Rotnam/PiTrac/docs/assets/images/camera/image3.jpg

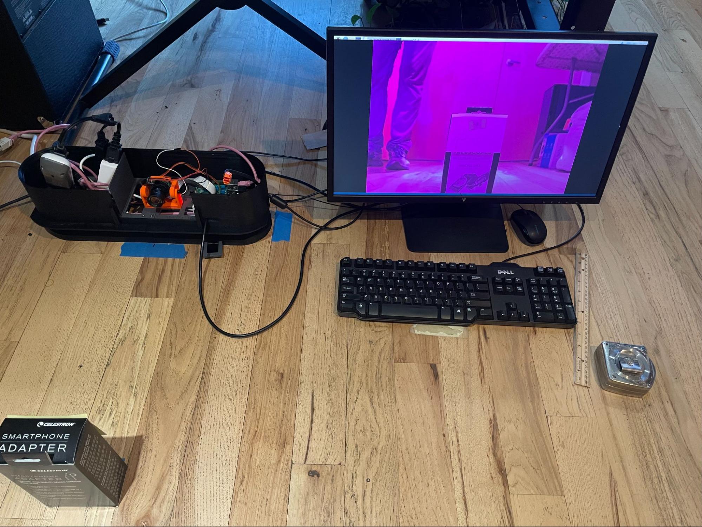
docs/assets/images/camera/image3.jpg
