Rotnam/PiTrac/docs/assets/images/camera/image4.jpg

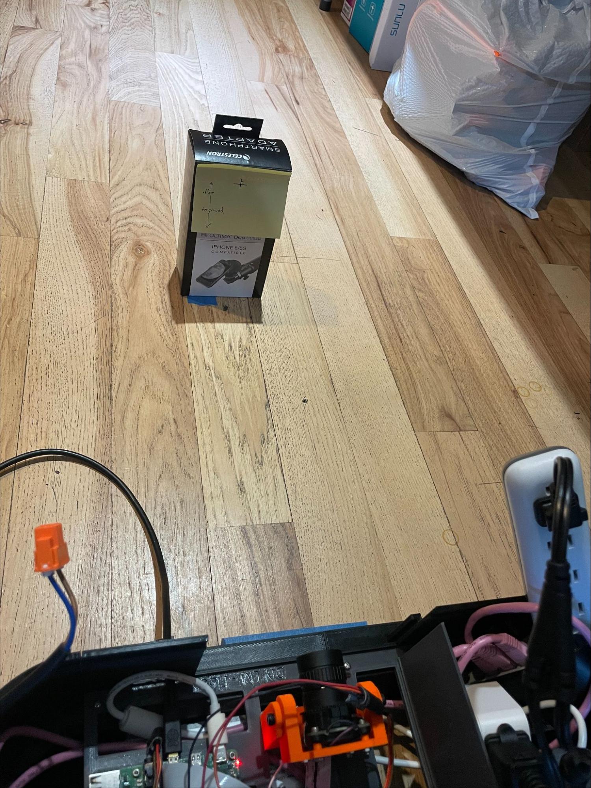
docs/assets/images/camera/image4.jpg
