Rotnam/PiTrac/docs/assets/images/camera/image7.jpg

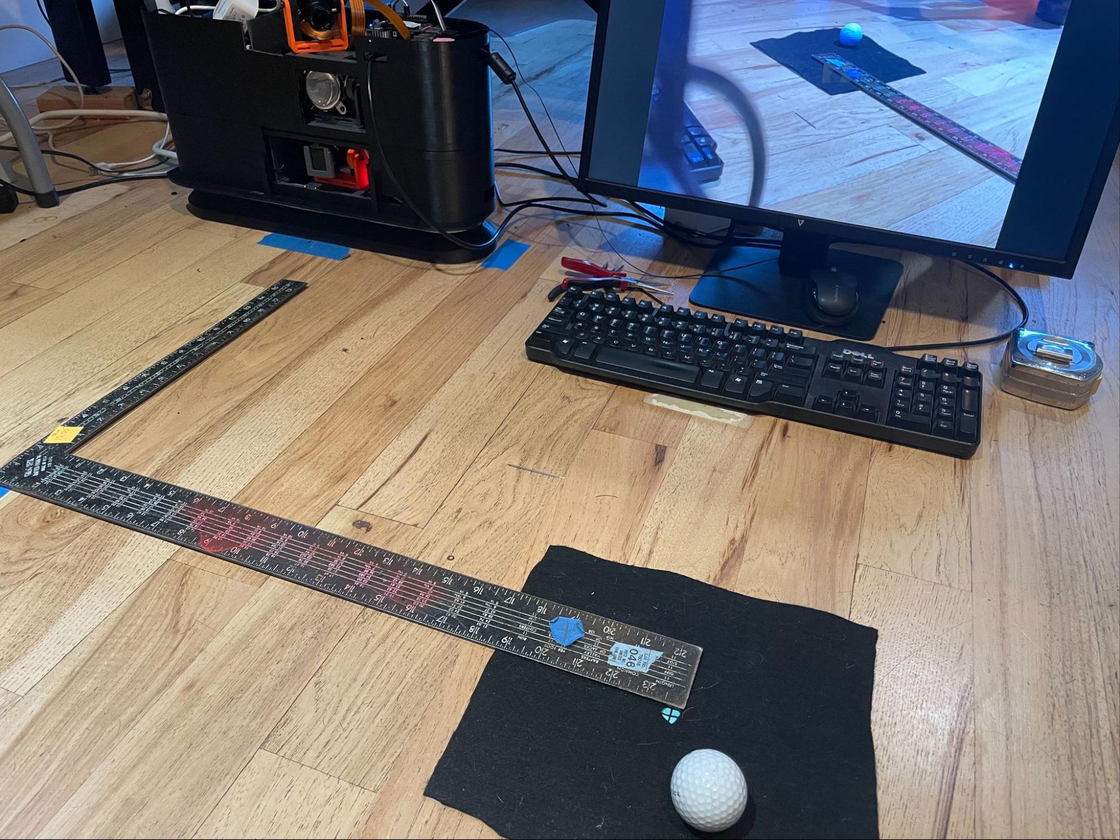
docs/assets/images/camera/image7.jpg
