Rotnam/PiTrac/docs/assets/images/camera/image8.png

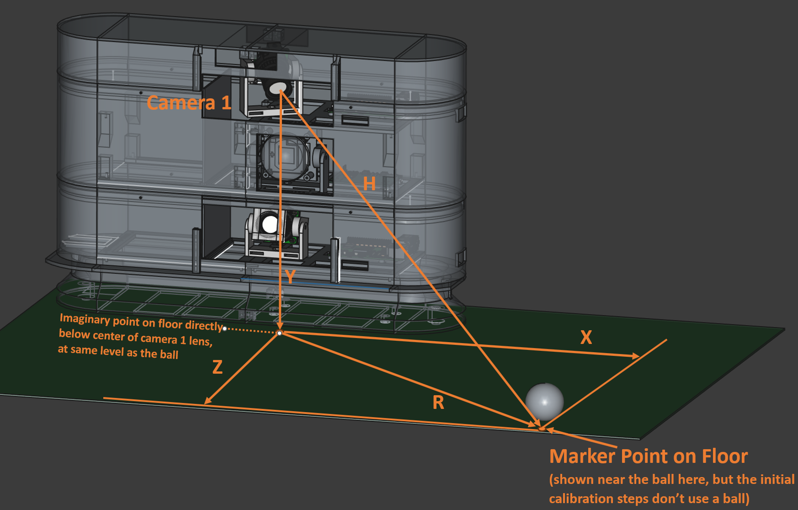
docs/assets/images/camera/image8.png
