Rotnam/PiTrac/docs/assets/images/camera/image9.jpg

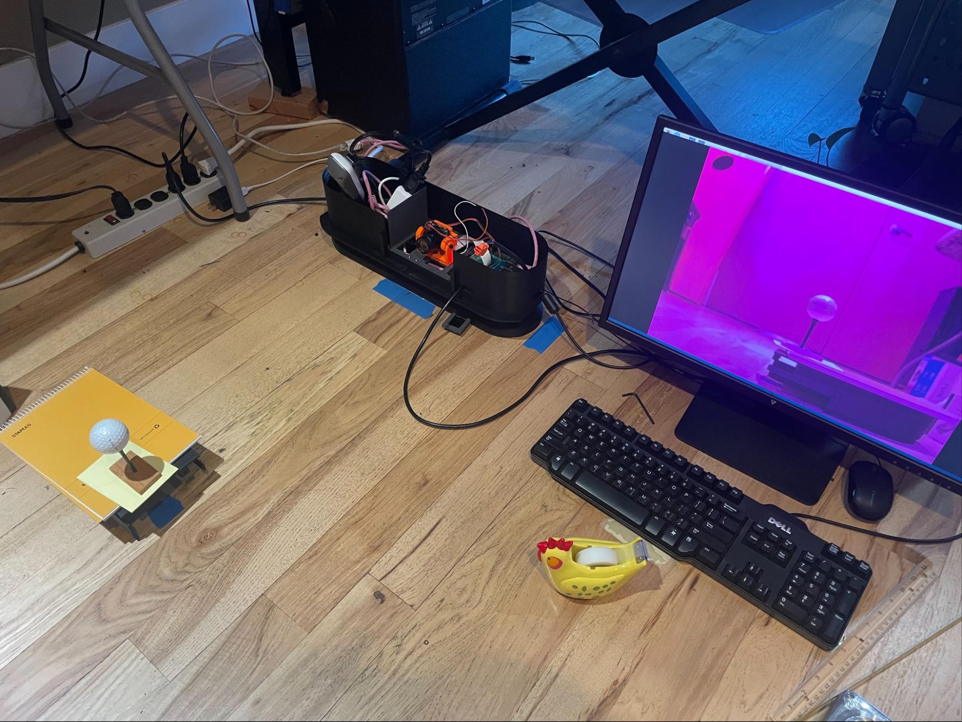
docs/assets/images/camera/image9.jpg
