Rotnam/PiTrac/docs/assets/images/camera/image10.png

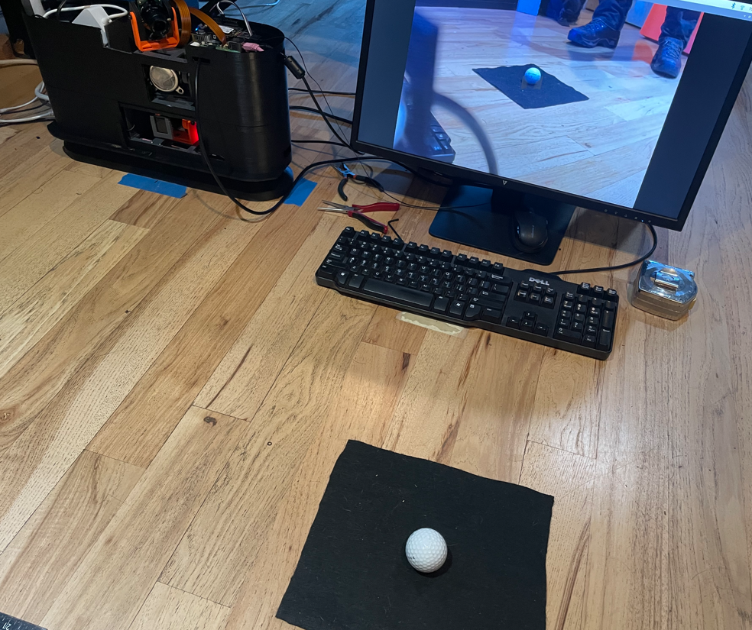
docs/assets/images/camera/image10.png
