Rotnam/PiTrac/3D Printed Parts/Enclosure Version 2/CaseCover/CaseCover - 3D Model.png

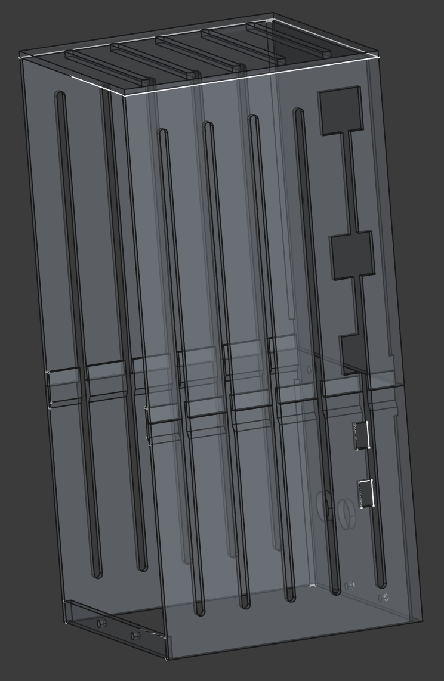
3D Printed Parts/Enclosure Version 2/CaseCover/CaseCover - 3D Model.png
