Rotnam/PiTrac/3D Printed Parts/Enclosure Version 2/CaseCover/CaseCover - Lower Half - Slicer Output.png

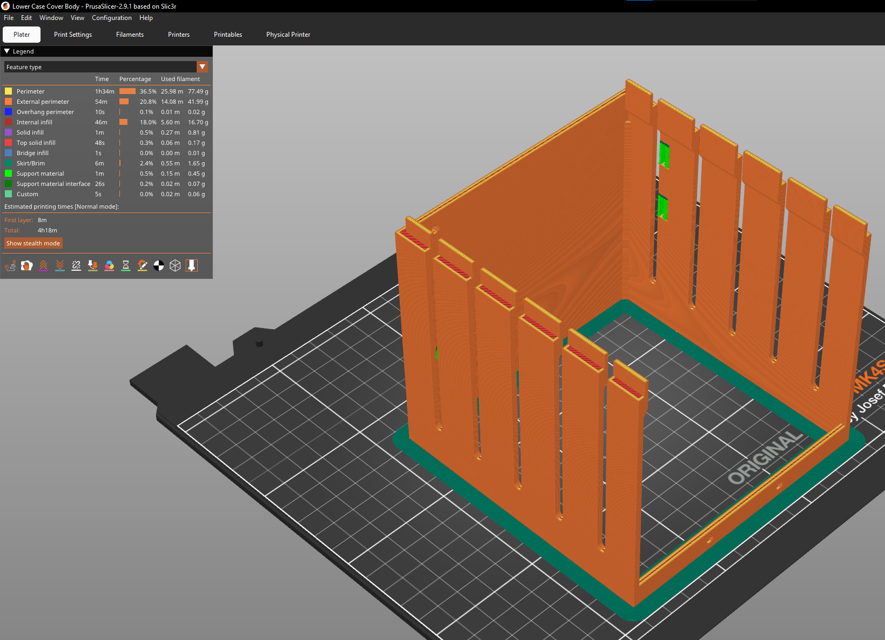
3D Printed Parts/Enclosure Version 2/CaseCover/CaseCover - Lower Half - Slicer Output.png
