Rotnam/PiTrac/3D Printed Parts/Enclosure Version 2/LED-Array-Strobe-Light-Mount/LED Strobe Mount - Slice Output.png

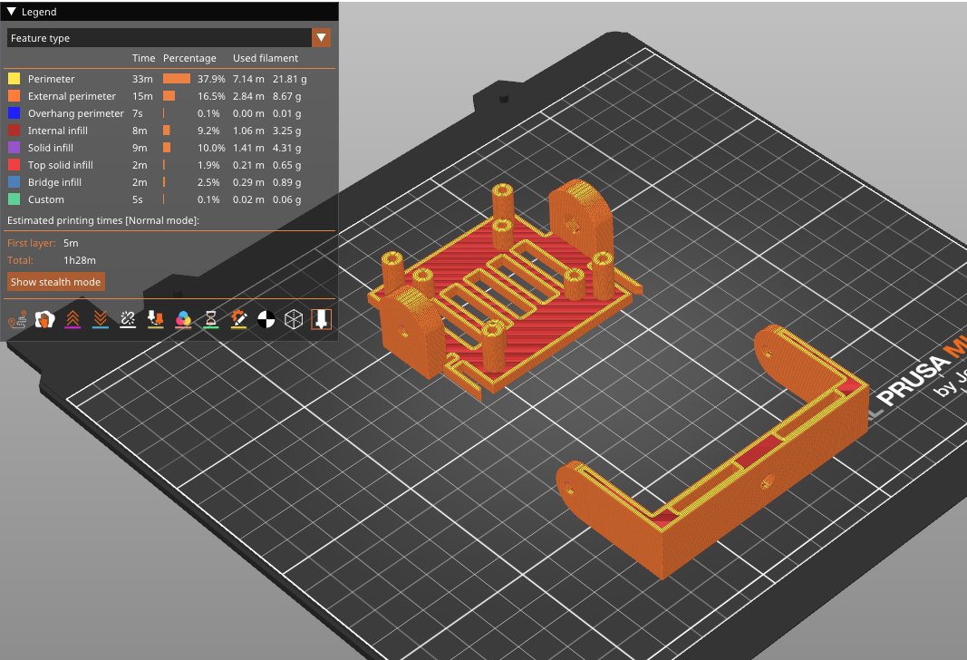
3D Printed Parts/Enclosure Version 2/LED-Array-Strobe-Light-Mount/LED Strobe Mount - Slice Output.png
