Rotnam/PiTrac/3D Printed Parts/Enclosure Version 2/Pi-Camera-Light-Filter-Holder/Filter Holder - 3D Model.png

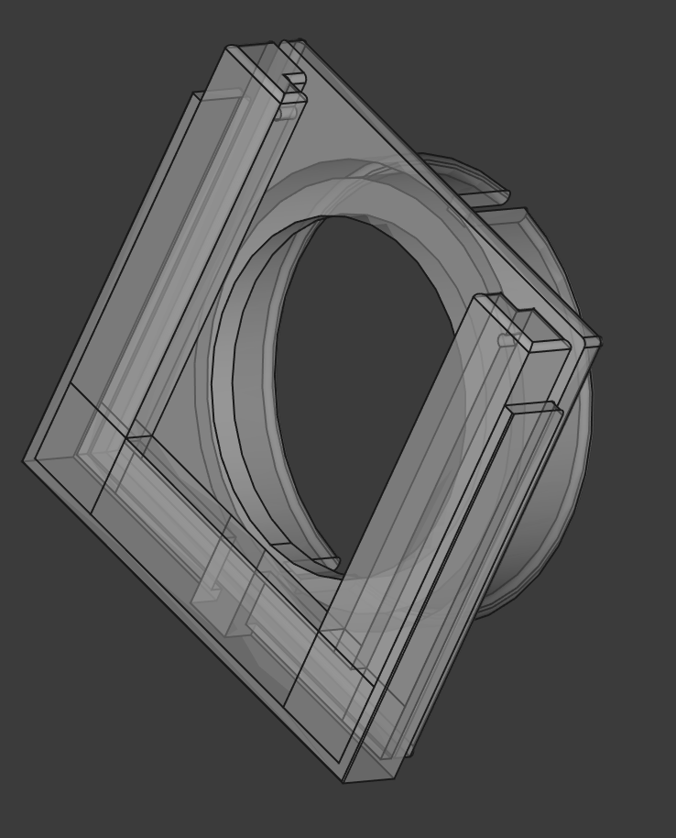
3D Printed Parts/Enclosure Version 2/Pi-Camera-Light-Filter-Holder/Filter Holder - 3D Model.png
