Rotnam/PiTrac/3D Printed Parts/Enclosure Version 2/Pi-Camera-Mounts/Pi Camera Mount - Bottom Variation - Slicer Output.png

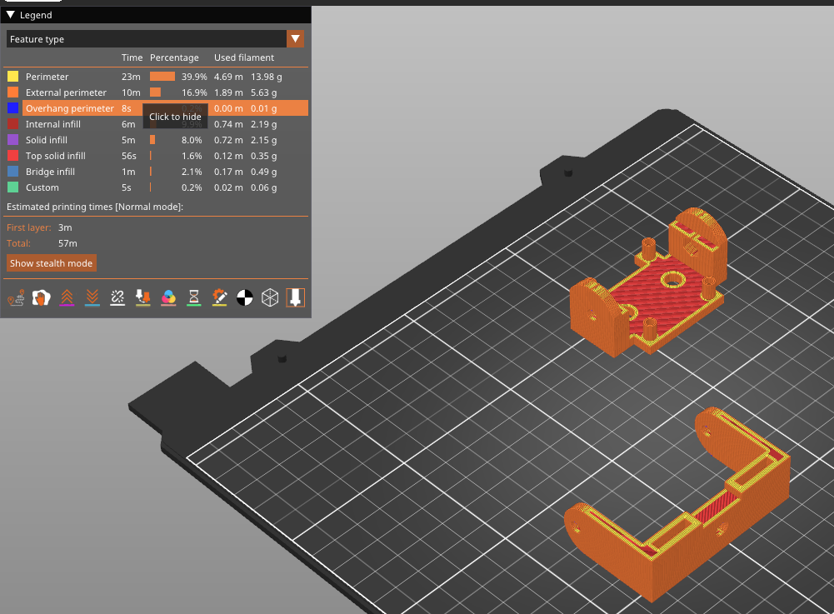
3D Printed Parts/Enclosure Version 2/Pi-Camera-Mounts/Pi Camera Mount - Bottom Variation - Slicer Output.png
