Rotnam/PiTrac/3D Printed Parts/Enclosure Version 2/Pi-Camera-Mounts/Pi Camera Mount - Example Variations.png

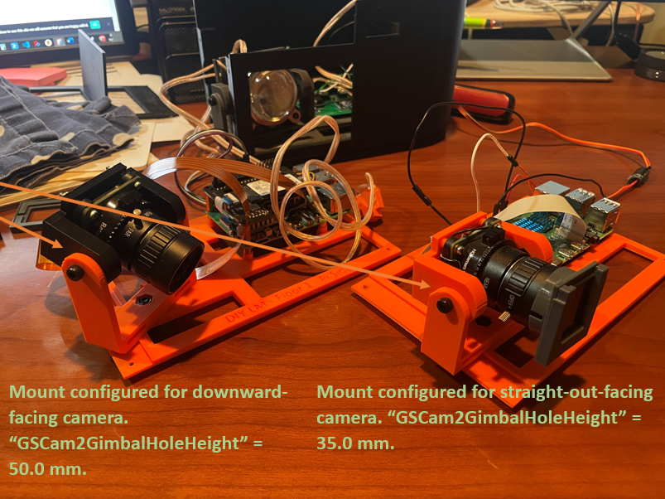
3D Printed Parts/Enclosure Version 2/Pi-Camera-Mounts/Pi Camera Mount - Example Variations.png
