Rotnam/PiTrac/3D Printed Parts/Enclosure Version 2/Tower-Connector-Board-Variant/Backplate- Connector Board Variant - Slicer Output.png

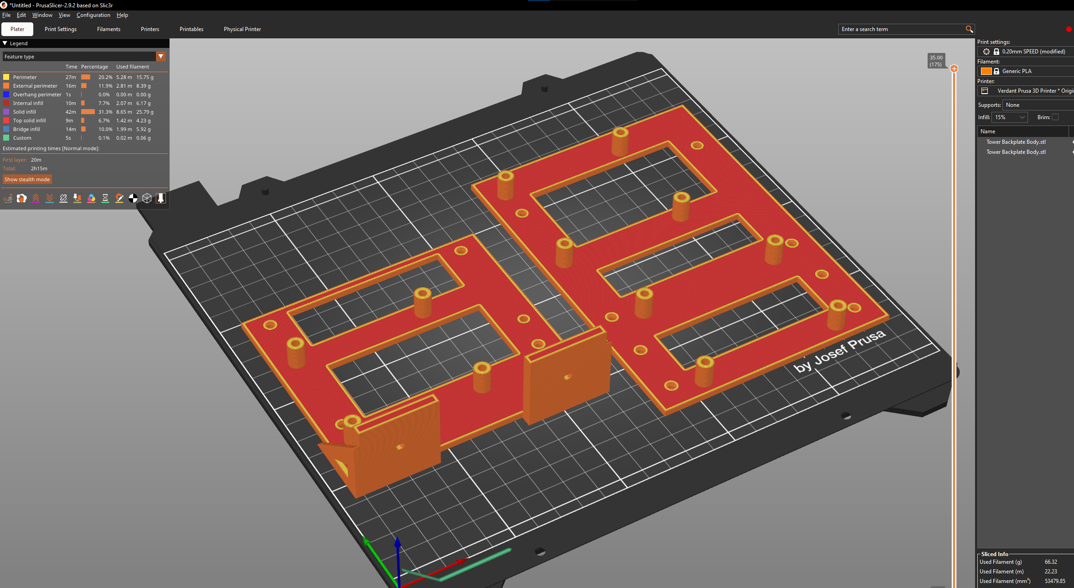
3D Printed Parts/Enclosure Version 2/Tower-Connector-Board-Variant/Backplate- Connector Board Variant - Slicer Output.png
