Rotnam/PiTrac/3D Printed Parts/Enclosure Version 2/Tower-Connector-Board-Variant/Frontplate Split Example - Prusa.png

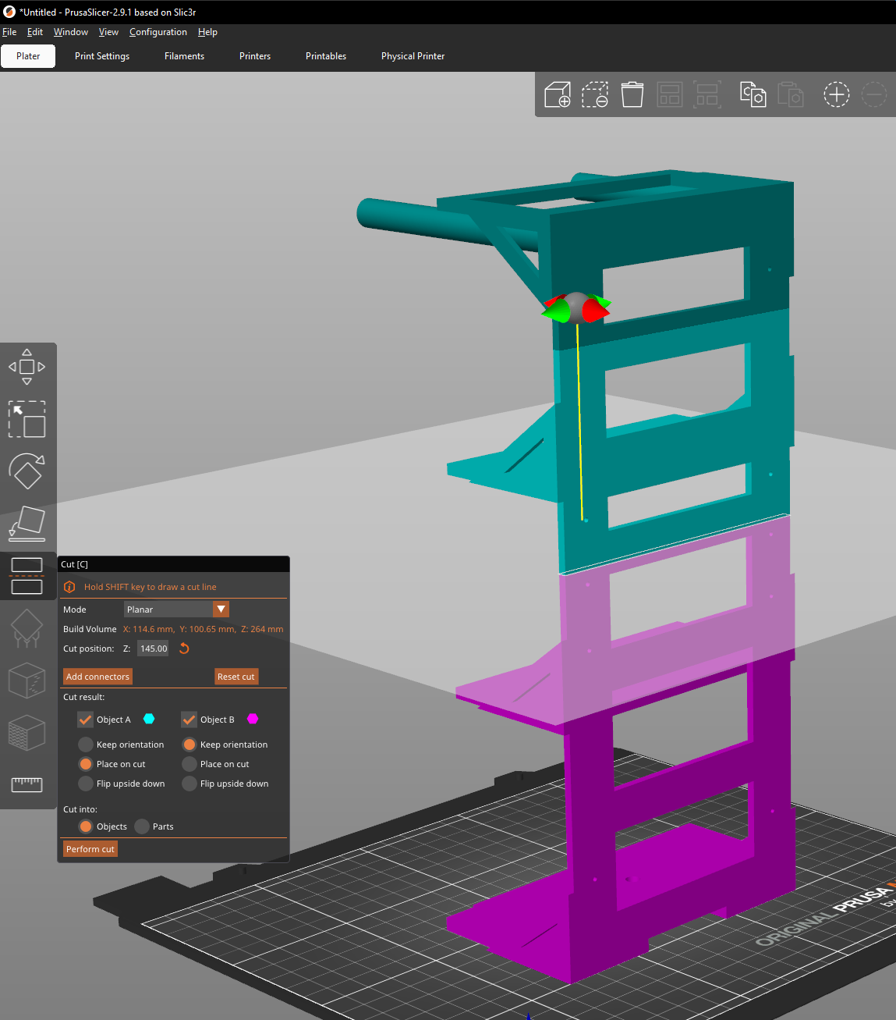
3D Printed Parts/Enclosure Version 2/Tower-Connector-Board-Variant/Frontplate Split Example - Prusa.png
