Rotnam/PiTrac/3D Printed Parts/Enclosure Version 2/Tower/Tower - Frontplate- Slicer Output.png

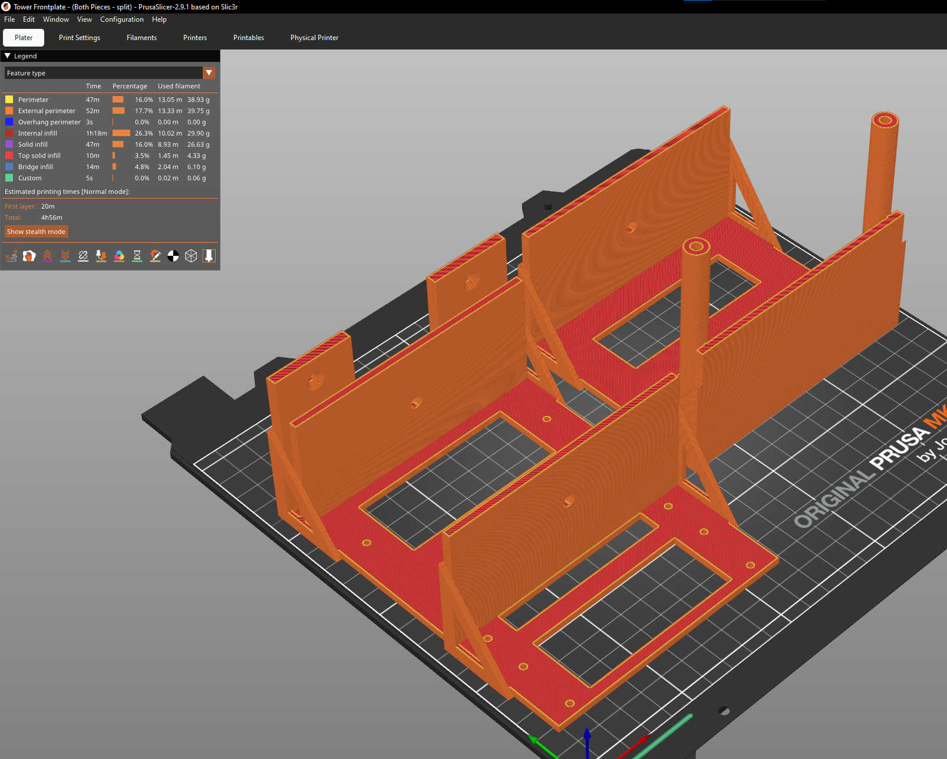
3D Printed Parts/Enclosure Version 2/Tower/Tower - Frontplate- Slicer Output.png
