Rotnam/PiTrac/3D Printed Parts/Enclosure Version 2/Integrated Enclosure (DO NOT PRINT)/Integrated PiTrac.FCStd

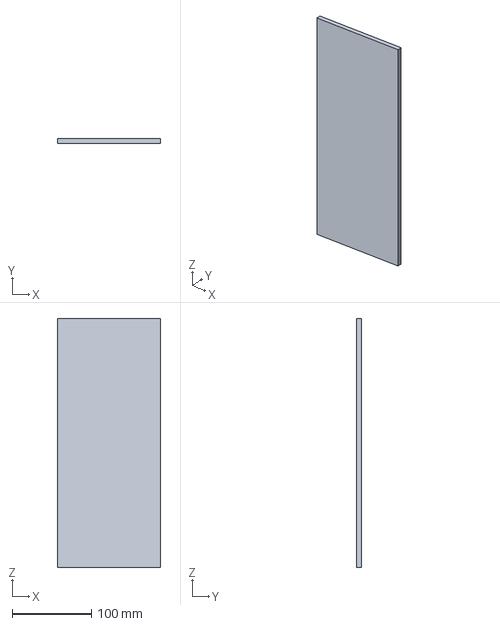
[picture p46: CAD file, 2025-04-05]
3D Printed Parts/Enclosure Version 2/Integrated Enclosure (DO NOT PRINT)/Integrated PiTrac.FCStd
130.0 x 6.35 x 315.0 mm
