Rotnam/PiTrac/3D Printed Parts/Enclosure Version 2/Pi-Camera-Mounts/Camera Mount - Bottom.FCStd

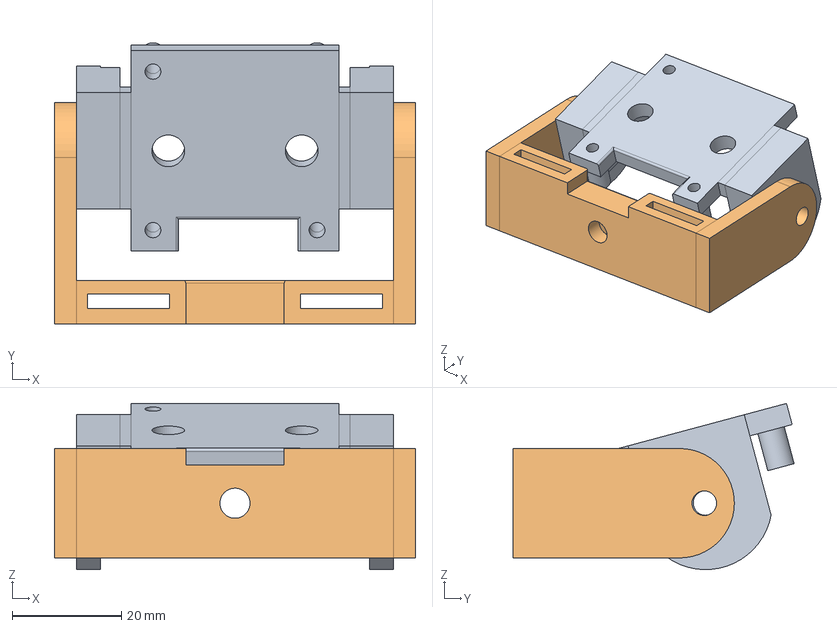
[picture p47: CAD file, 2025-04-05]
3D Printed Parts/Enclosure Version 2/Pi-Camera-Mounts/Camera Mount - Bottom.FCStd
66.0 x 51.4 x 30.4 mm
Back Plate Body
Gimbal Base Body
