Rotnam/PiTrac/3D Printed Parts/Enclosure Version 2/Tower/Tower Frontplate - (Both Pieces - split).3mf

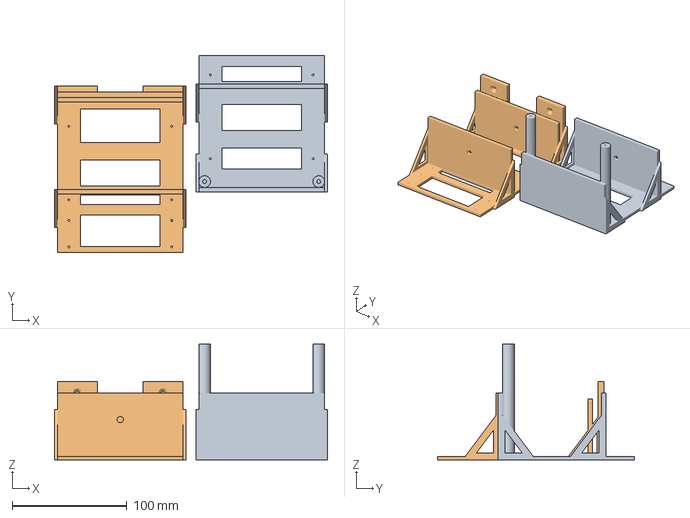
[picture p48: CAD file, 2025-04-05]
3D Printed Parts/Enclosure Version 2/Tower/Tower Frontplate - (Both Pieces - split).3mf
237.8 x 171.8 x 100.7 mm
Backplate-Tower Frontplate Body.stl x 2
