Rotnam/PiTrac/3D Printed Parts/Miscellaneous 3D Parts/m2-nvme-clip/m2nvme-clip v2.3mf

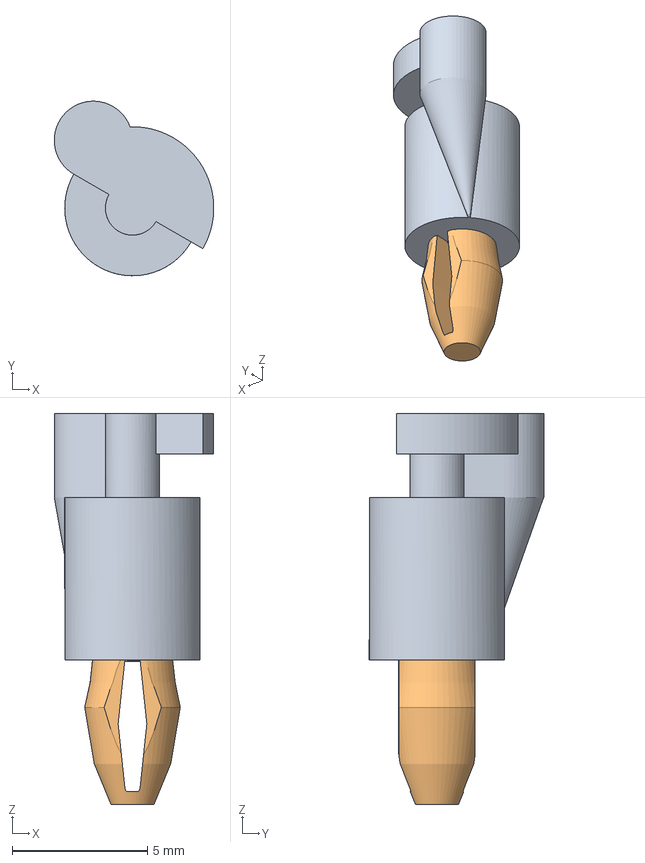
[picture p49: CAD file, 2025-02-07]
3D Printed Parts/Miscellaneous 3D Parts/m2-nvme-clip/m2nvme-clip v2.3mf
5.89 x 6.44 x 14.4 mm
m2
micro_pci_pcb_spacer
