Rotnam/PiTrac/3D Printed Parts/Enclosure Version 2/BaseBox/BaseBox.FCStd

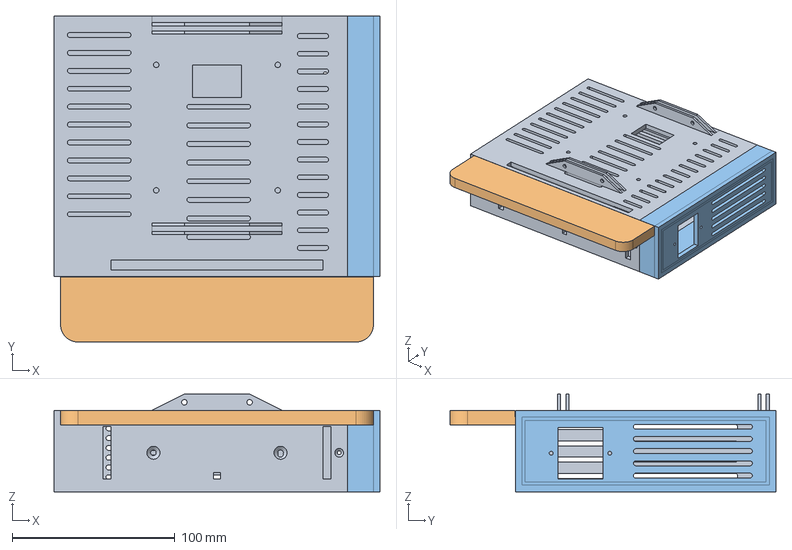
[picture p50: CAD file, 2025-04-05]
3D Printed Parts/Enclosure Version 2/BaseBox/BaseBox.FCStd
200.0 x 200.1 x 60.0 mm
BaseBox Body
Light Shield Body
Cap Body
