Rotnam/PiTrac/3D Printed Parts/Enclosure Version 2/Integrated Enclosure (DO NOT PRINT)/LRS-150.stp

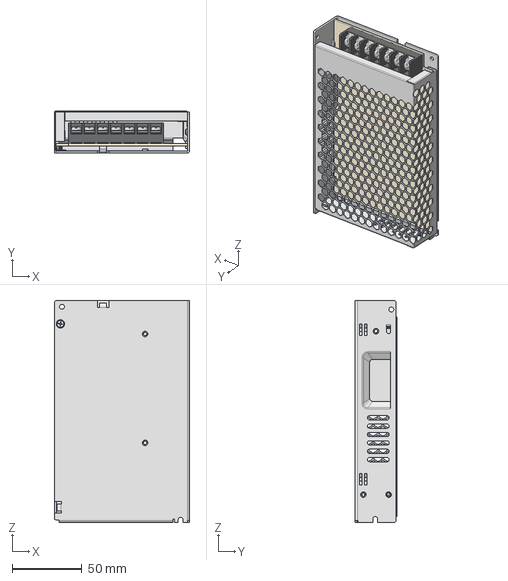
[picture p51: CAD file, 2025-04-05]
3D Printed Parts/Enclosure Version 2/Integrated Enclosure (DO NOT PRINT)/LRS-150.stp
97.0 x 30.0 x 159.0 mm
