Rotnam/PiTrac/3D Printed Parts/Enclosure Version 2/Pi-Camera-Mounts/Camera Mount - Top Variation.3mf

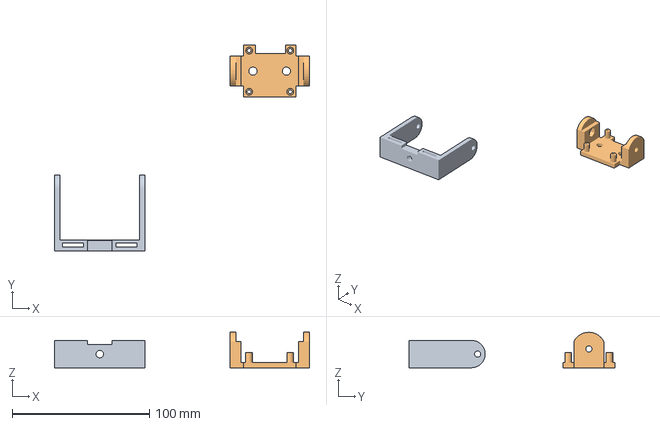
[picture p52: CAD file, 2025-04-05]
3D Printed Parts/Enclosure Version 2/Pi-Camera-Mounts/Camera Mount - Top Variation.3mf
185.9 x 150.1 x 25.9 mm
Camera Mount - Top Variation.stl_1
Camera Mount - Top Variation.stl_2
