Rotnam/PiTrac/3D Printed Parts/Enclosure Version 2/Tower-Connector-Board-Variant/Tower Frontplate Body - Connector Board Variant - Split Pieces.3mf

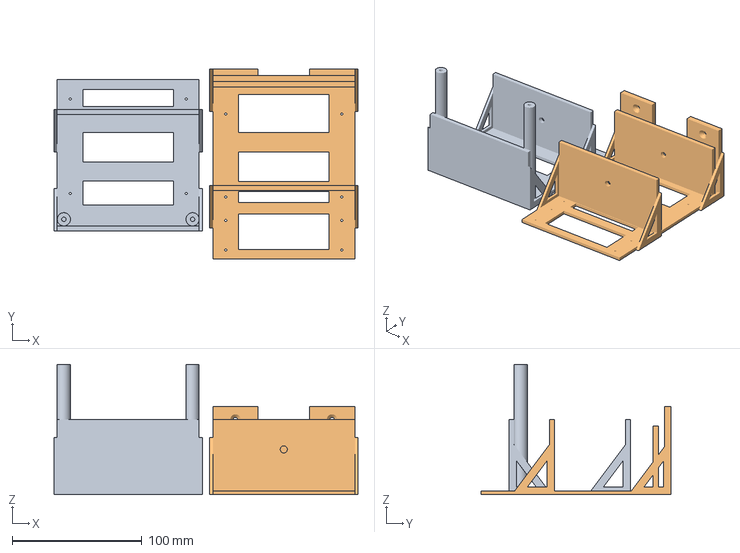
[picture p53: CAD file, 2025-04-16]
3D Printed Parts/Enclosure Version 2/Tower-Connector-Board-Variant/Tower Frontplate Body - Connector Board Variant - Split Pieces.3mf
234.7 x 147.0 x 100.6 mm
Tower Frontplate Body.stl x 2
