Rotnam/PiTrac/3D Printed Parts/Enclosure Version 2/Tower/Tower Backplate Body.stl

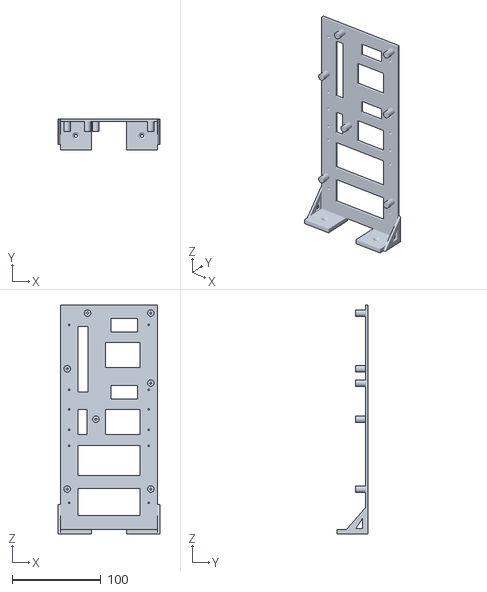
[picture p54: CAD file, 2025-04-05]
3D Printed Parts/Enclosure Version 2/Tower/Tower Backplate Body.stl
114.6 x 35.0 x 257.6
