Rotnam/PiTrac/3D Printed Parts/Enclosure Version 2/CaseCover/Lower Case Cover Body.3mf

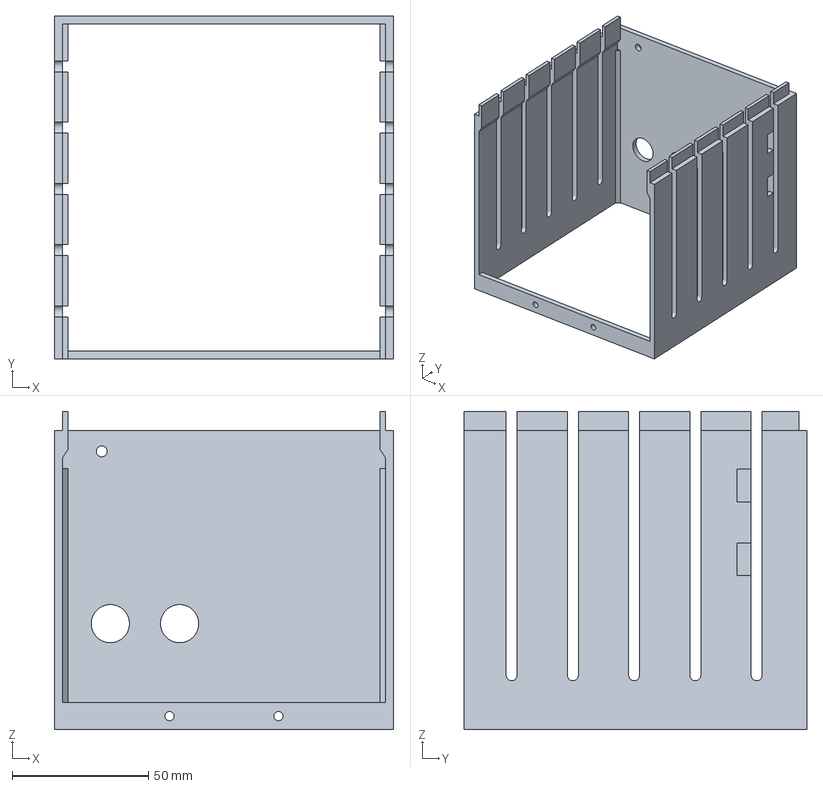
[picture p55: CAD file, 2025-04-05]
3D Printed Parts/Enclosure Version 2/CaseCover/Lower Case Cover Body.3mf
124.6 x 126.0 x 117.0 mm
