Rotnam/PiTrac/3D Printed Parts/Enclosure Version 2/Integrated Enclosure (DO NOT PRINT)/Cree LED Lens.FCStd

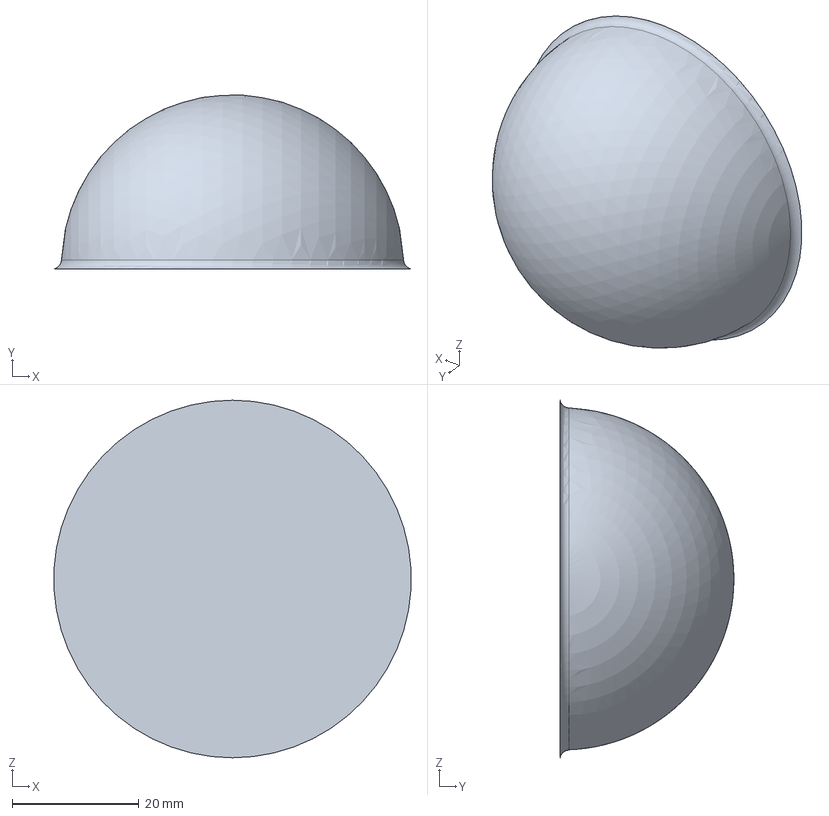
[picture p56: CAD file, 2025-04-05]
3D Printed Parts/Enclosure Version 2/Integrated Enclosure (DO NOT PRINT)/Cree LED Lens.FCStd
56.3 x 27.4 x 56.4 mm
