Rotnam/PiTrac/3D Printed Parts/Enclosure Version 2/Tower-Connector-Board-Variant/Tower Backplate Body - Connector Board Variant - Split Pieces.3mf

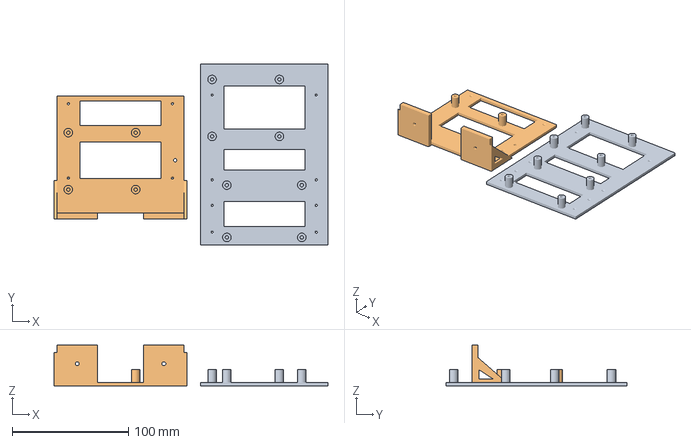
[picture p57: CAD file, 2025-04-16]
3D Printed Parts/Enclosure Version 2/Tower-Connector-Board-Variant/Tower Backplate Body - Connector Board Variant - Split Pieces.3mf
235.9 x 156.0 x 35.0 mm
Tower Backplate Body.stl x 2
