Rotnam/PiTrac/3D Printed Parts/Enclosure Version 2/Pi-Camera-Mounts/Camera Mount - Top Variation (Cam1).FCStd

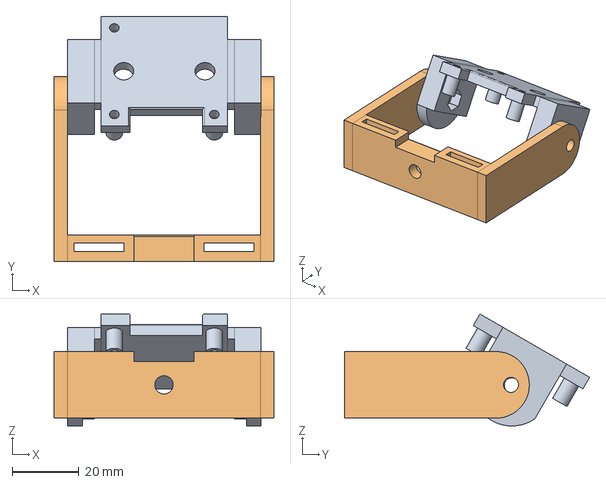
[picture p58: CAD file, 2025-04-05]
3D Printed Parts/Enclosure Version 2/Pi-Camera-Mounts/Camera Mount - Top Variation (Cam1).FCStd
66.0 x 73.6 x 33.6 mm
Back Plate Body
Gimbal
