Rotnam/PiTrac/3D Printed Parts/Enclosure Version 2/Tower-Connector-Board-Variant/Tower Backplate Body.stl

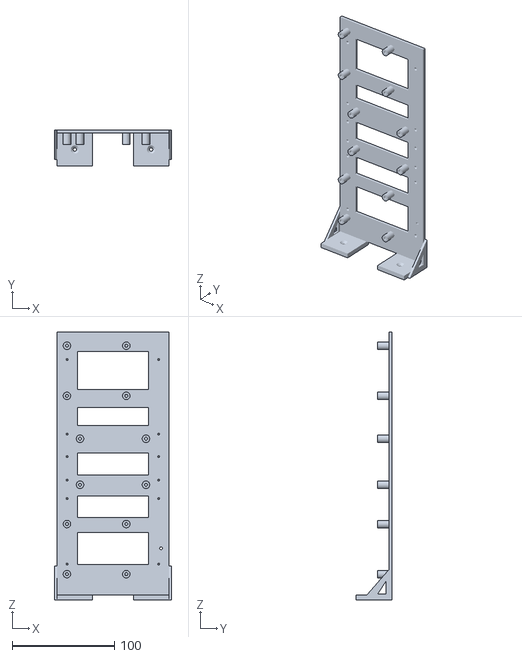
[picture p59: CAD file, 2025-04-16]
3D Printed Parts/Enclosure Version 2/Tower-Connector-Board-Variant/Tower Backplate Body.stl
114.6 x 35.0 x 262.0
