Rotnam/PiTrac/3D Printed Parts/Enclosure Version 2/Tower/Tower Backplate Bodies (Both pieces - split).3mf

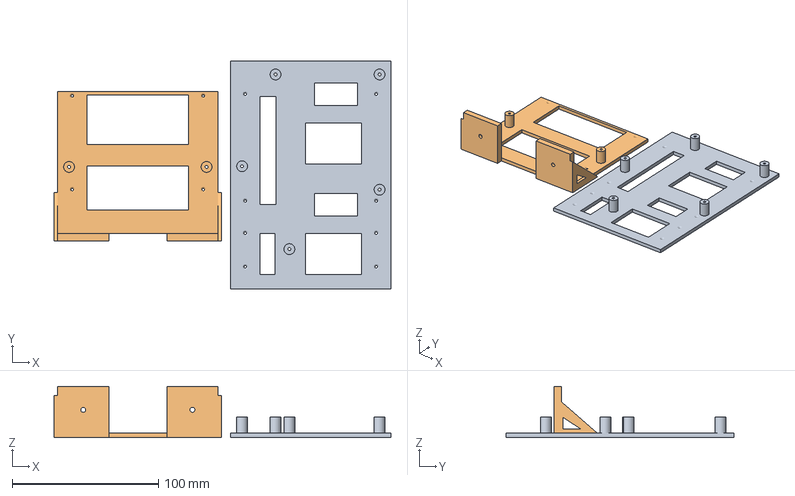
[picture p60: CAD file, 2025-04-05]
3D Printed Parts/Enclosure Version 2/Tower/Tower Backplate Bodies (Both pieces - split).3mf
230.4 x 155.6 x 35.0 mm
Tower Backplate Body.stl x 2
