Rotnam/PiTrac/3D Printed Parts/Enclosure Version 2/Integrated Enclosure (DO NOT PRINT)/Cree LED.FCStd

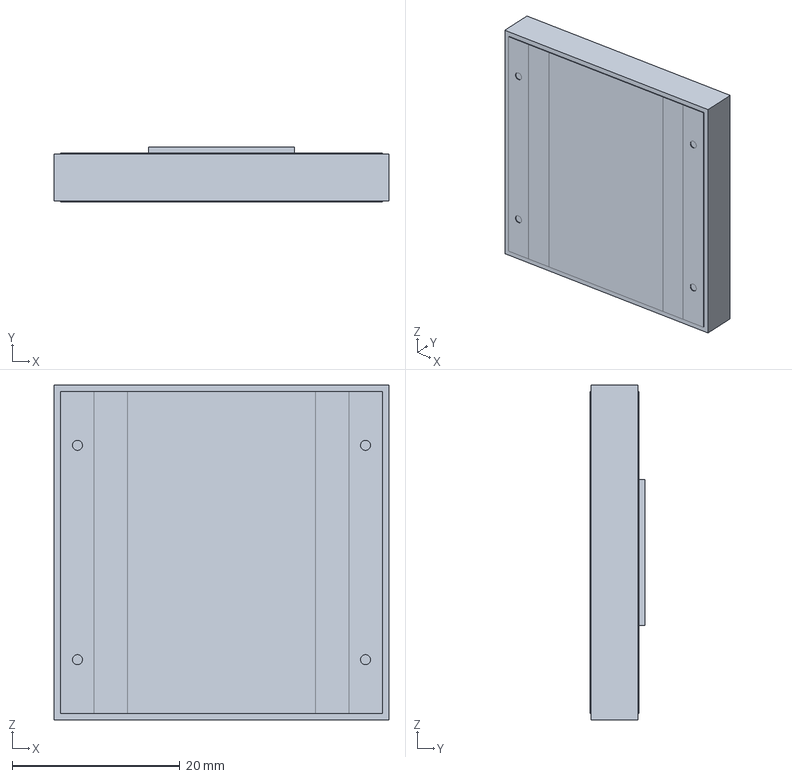
[picture p61: CAD file, 2025-04-05]
3D Printed Parts/Enclosure Version 2/Integrated Enclosure (DO NOT PRINT)/Cree LED.FCStd
40.0 x 6.52 x 40.0 mm
