Rotnam/PiTrac/3D Printed Parts/Enclosure Version 2/BaseBox/BaseBox-End Cap.3mf

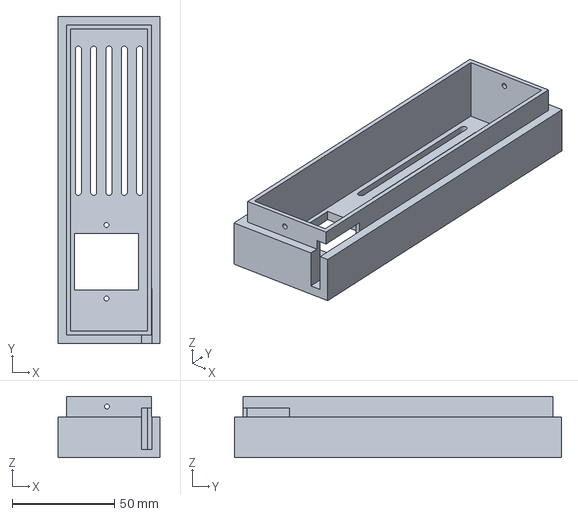
[picture p62: CAD file, 2025-04-05]
3D Printed Parts/Enclosure Version 2/BaseBox/BaseBox-End Cap.3mf
50.0 x 160.0 x 30.0 mm
