Rotnam/PiTrac/3D Printed Parts/Enclosure Version 2/Pi-Camera-Mounts/Camera Mounts - Printed Examples.jpg

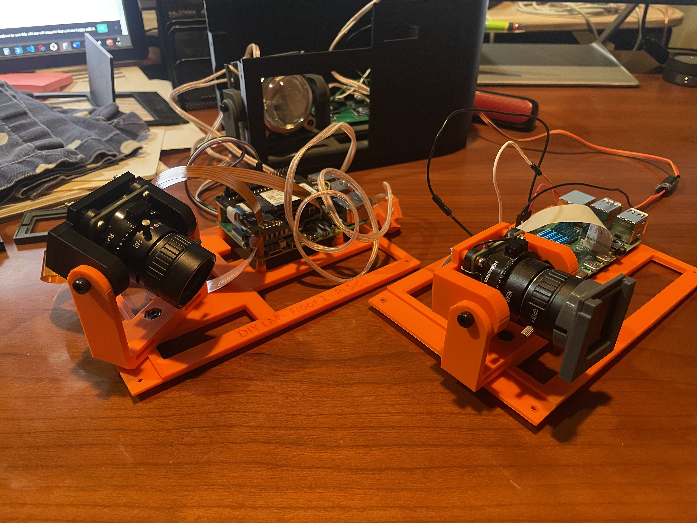
3D Printed Parts/Enclosure Version 2/Pi-Camera-Mounts/Camera Mounts - Printed Examples.jpg
