Rotnam/PiTrac/Software/LMSourceCode/Testing/Left-Handed-Shots/clear_strobed_img_LEFT.png

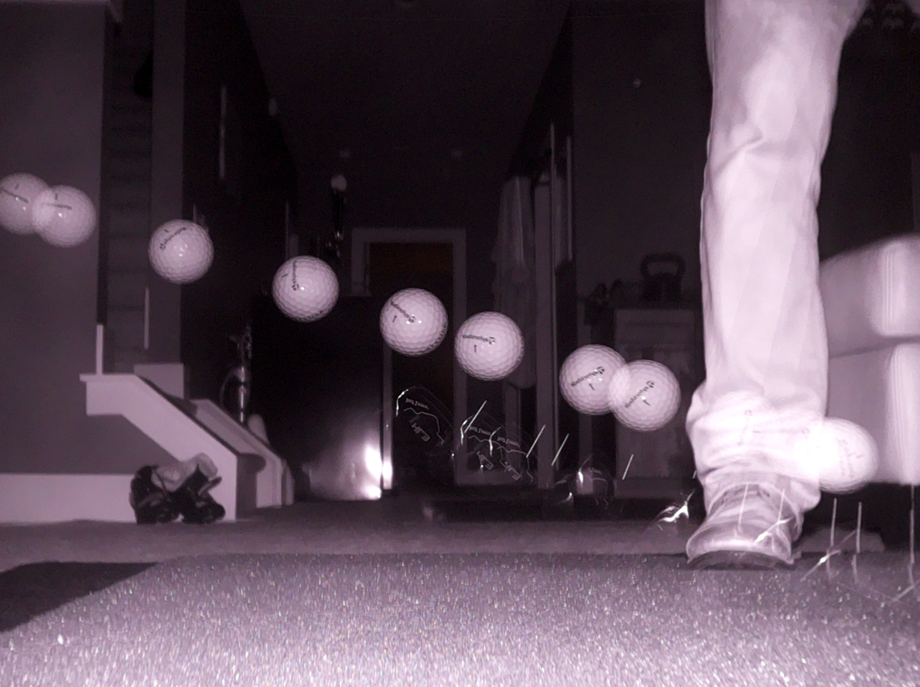
Software/LMSourceCode/Testing/Left-Handed-Shots/clear_strobed_img_LEFT.png
