Rotnam/PiTrac/Software/LMSourceCode/Testing/Left-Handed-Shots/gs_log_img__log_ball_final_found_ball_img_Shot_7_2025-Feb-18_18.23.22.png

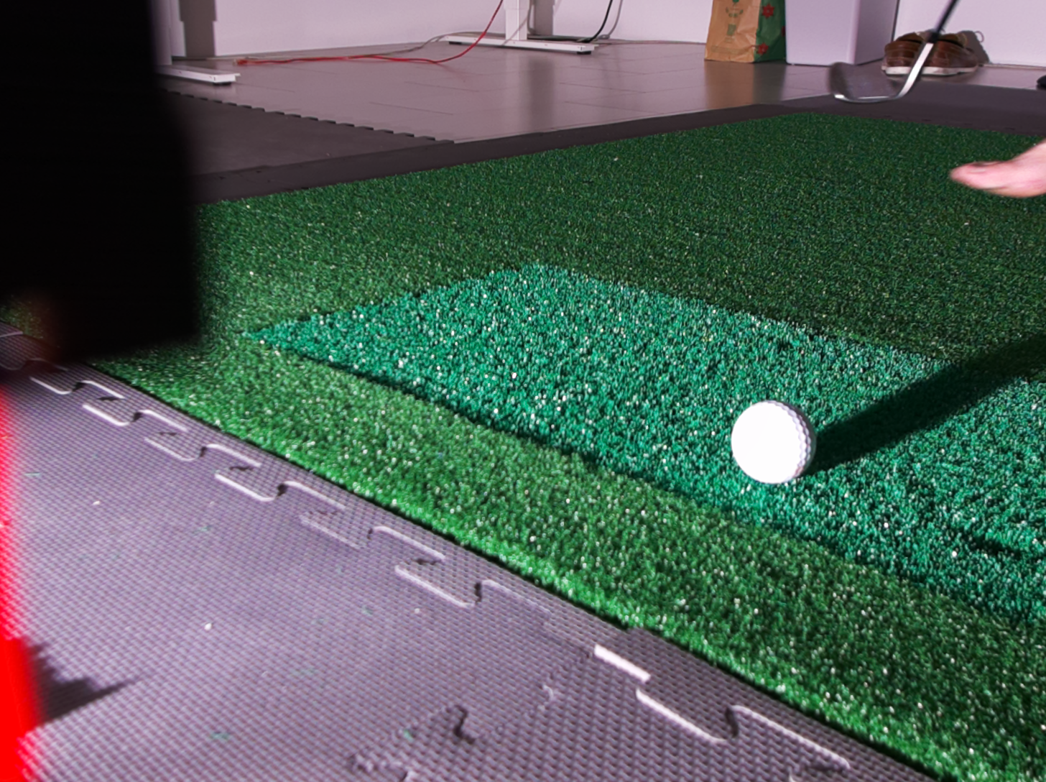
Software/LMSourceCode/Testing/Left-Handed-Shots/gs_log_img__log_ball_final_found_ball_img_Shot_7_2025-Feb-18_18.23.22.png
