Rotnam/PiTrac/Software/LMSourceCode/Testing/Left-Handed-Shots/gs_log_img__log_cam2_last_strobed_img_Shot_1_2025-Feb-07_11.03.12_LEFT_HANDED.png

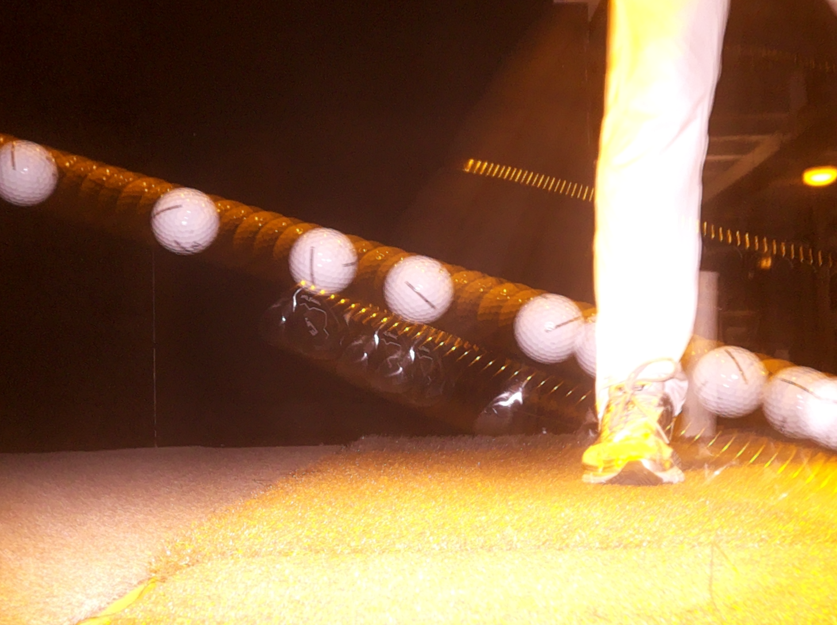
Software/LMSourceCode/Testing/Left-Handed-Shots/gs_log_img__log_cam2_last_strobed_img_Shot_1_2025-Feb-07_11.03.12_LEFT_HANDED.png
