Rotnam/PiTrac/Software/LMSourceCode/Testing/TestSuite_2025_02_07/gs_log_img__log_cam2_last_strobed_img_Shot_1_2025-Feb-07_11.03.12.png

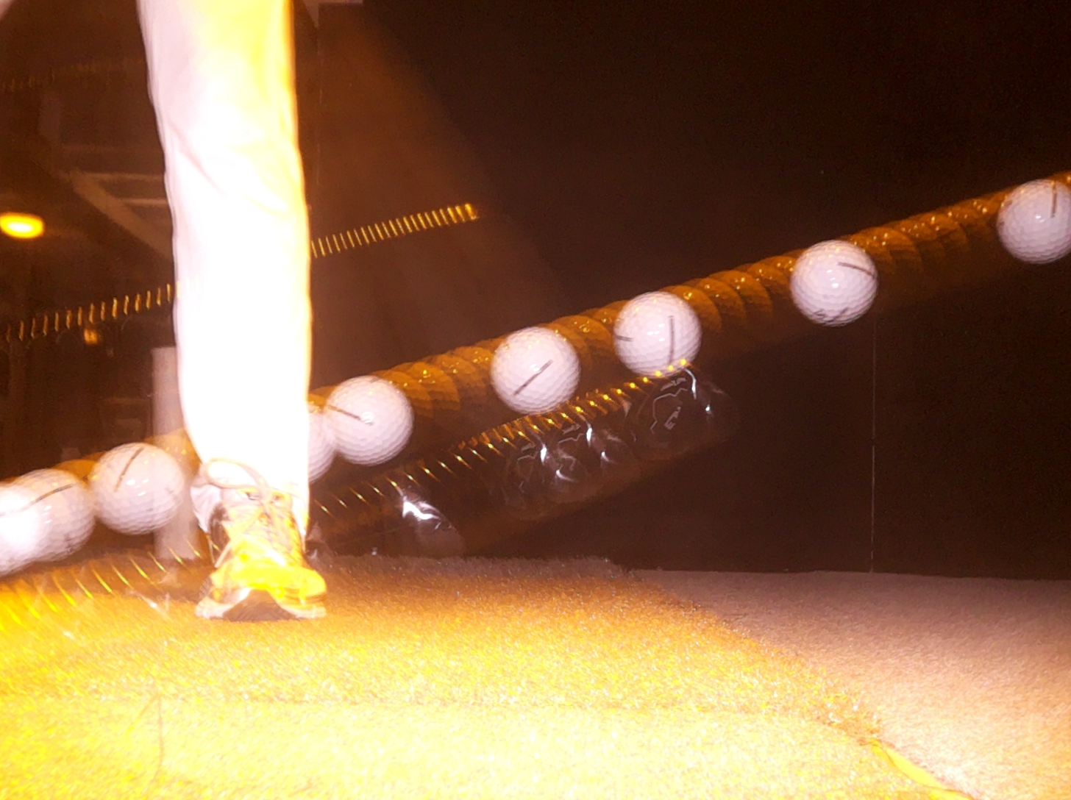
Software/LMSourceCode/Testing/TestSuite_2025_02_07/gs_log_img__log_cam2_last_strobed_img_Shot_1_2025-Feb-07_11.03.12.png
