Rotnam/PiTrac/Software/LMSourceCode/Testing/TestSuite_2025_02_07/gs_log_img__log_cam2_last_strobed_img_Shot_2_2025-Feb-07_11.04.22.png

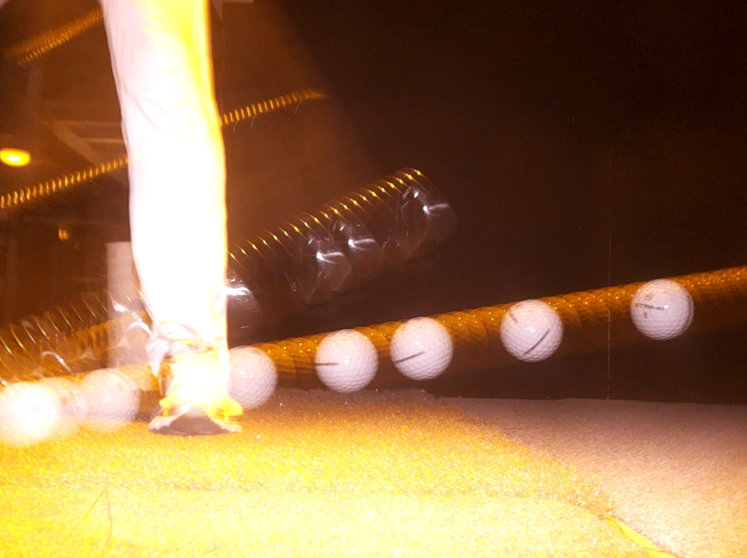
Software/LMSourceCode/Testing/TestSuite_2025_02_07/gs_log_img__log_cam2_last_strobed_img_Shot_2_2025-Feb-07_11.04.22.png
